luissaya/UV_reader/firmware/block_codes/deepsleep/deepsleep.ino

/*
 * ESP8266 Deep sleep mode example
 * Rui Santos 
 * Complete Project Details https://randomnerdtutorials.com
 */
#define led D4
void setup() {
  Serial.begin(115200);
  delay(2000);
  pinMode(led, OUTPUT);

  // Wait for serial to initialize.
  Serial.println("Led on");
  digitalWrite(led, HIGH);   // turn the LED on (HIGH is the voltage level)
  delay(100);               // wait for a second
  Serial.println("Led off");
  digitalWrite(led, LOW);    // turn the LED off by making the voltage LOW
  delay(100);               // wait for a second
  Serial.println("Led on");
  digitalWrite(led, HIGH);   // turn the LED on (HIGH is the voltage level)
  delay(100);               // wait for a second
  Serial.println("Led off");
  digitalWrite(led, LOW);    // turn the LED off by making the voltage LOW
  delay(100);               // wait for a second
  
  // Deep sleep mode for 30 seconds, the ESP8266 wakes up by itself when GPIO 16 (D0 in NodeMCU board) is connected to the RESET pin
  Serial.println("I'm awake, but I'm going into deep sleep mode for 5 seconds");
  ESP.deepSleep(3e6); 
  
  // Deep sleep mode until RESET pin is connected to a LOW signal (for example pushbutton or magnetic reed switch)
  //Serial.println("I'm awake, but I'm going into deep sleep mode until RESET pin is connected to a LOW signal");
  //ESP.deepSleep(0); 
}  

void loop() {
}
